Finalstepbitcoin/prisma/qr_canale.py

"""
Codice QR del canale - GENERATO AUTOMATICAMENTE, non modificare a mano.

Indirizzo: https://www.youtube.com/@final_step_bitcoin
Versione:  4, correzione Q, 33 moduli di lato
SHA-256:   8953a1871747566a9b07ac1bc8374f16c2b5773bd34f09f34a19eac4154011c9

Ogni riga e' fatta di 1 (modulo scuro) e 0 (modulo chiaro).
Per rigenerarlo:  .venv-strumenti/bin/python prepara_qr.py
"""

INDIRIZZO = "https://www.youtube.com/@final_step_bitcoin"
LATO = 33
MODULI = (
    "111111100010001010100110001111111",
    "100000101010100011010100001000001",
    "101110100000110101100110101011101",
    "101110101000101000001101101011101",
    "101110101001111110101000001011101",
    "100000100110000110000101001000001",
    "111111101010101010101010101111111",
    "000000001111101100011011000000000",
    "010111101101001011010001011011010",
    "011110000010010110110101000011100",
    "000100111101101001101101110011111",
    "010110011000101111011000011100100",
    "010011110010111001101000001010011",
    "110011001000011110011010000101100",
    "111001100101100010010100101110000",
    "001100000110101000110000110101101",
    "110100110000111000011011111111000",
    "010010010111110100110000111010100",
    "000100101101100100010101011101101",
    "100100010100000100110001000011100",
    "001100110001001000010000000101001",
    "110111001100110000010011010110000",
    "101100110011011110100111011000111",
    "100011001111000110000011011010111",
    "111110101010111101101001111111010",
    "000000001100110101000011100010110",
    "111111100110011101010011101010110",
    "100000101100101001011001100011111",
    "101110101001000100101011111110010",
    "101110101100100001011010010100001",
    "101110100111100101010100100111011",
    "100000101110000110100010001111111",
    "111111100111001010100001110110000",
)
